aburt2/EnchantiS3/enchantiS3-board/Screenshots/pcb_layout_bottom_layer.png

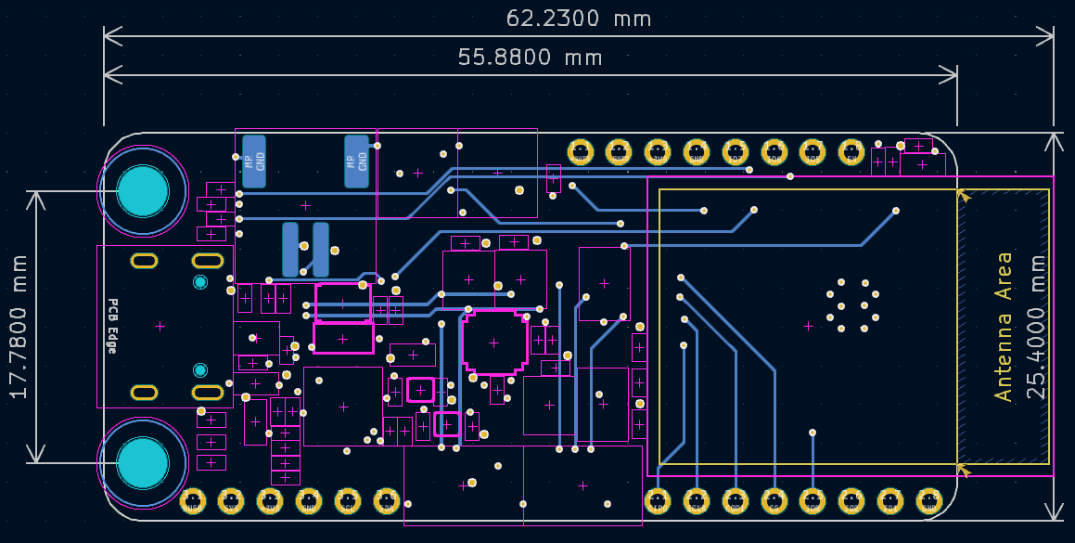
enchantiS3-board/Screenshots/pcb_layout_bottom_layer.png
