aburt2/EnchantiS3/enchantiS3-board/Screenshots/pcb_layout_power_layer.png

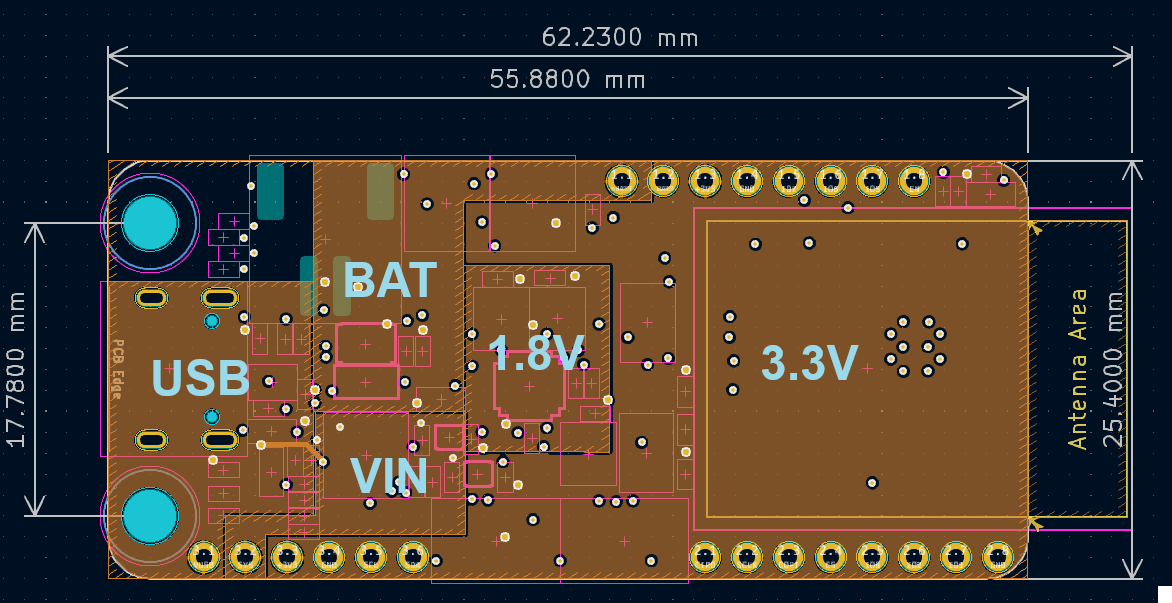
enchantiS3-board/Screenshots/pcb_layout_power_layer.png
