aburt2/EnchantiS3/enchantiS3-board/Screenshots/tstick-5gw-pro-USB-V2-pcb-back.png

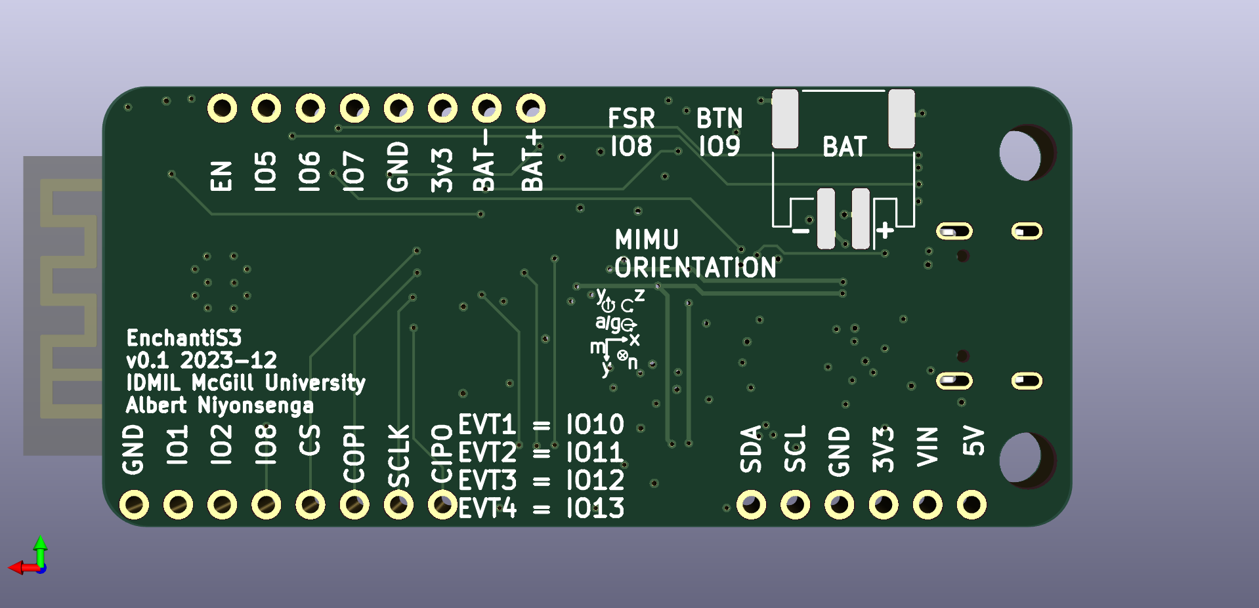
enchantiS3-board/Screenshots/tstick-5gw-pro-USB-V2-pcb-back.png
